suryaturaga3142/stargazing-vr/pcb-stargazing/3dmodels/usb4510-03-1-a.stp

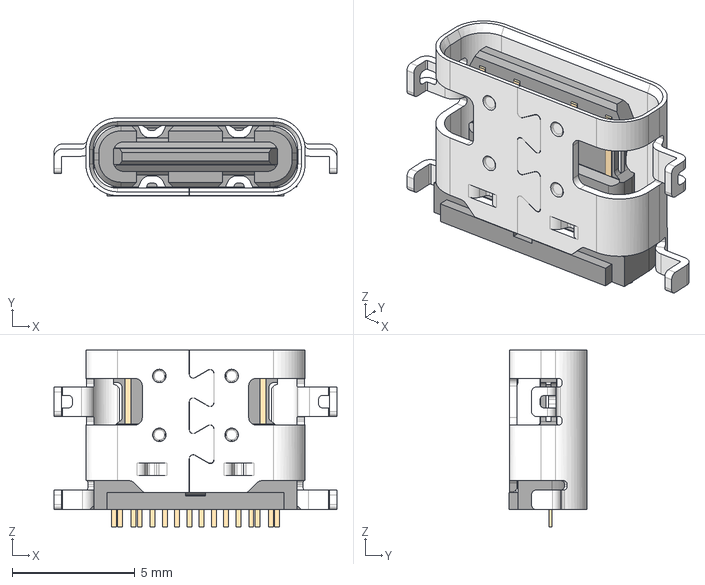
[picture p11: CAD file, 2025-11-23]
pcb-stargazing/3dmodels/usb4510-03-1-a.stp
11.5 x 3.18 x 7.20 mm
