suryaturaga3142/stargazing-vr/include/drivers/imu.h

/*******************************************************************************
 * @file        imu.h
 * @brief       Driver library for IMU.
 * @details     All functions needed to interact with BNO080 IMU.
 * 
 * @see         imu.c for implementation details.
 * 
 * @author      LED Chasers
 * @date        2025-10-14
 * @version     1.0
 ******************************************************************************/

#ifndef IMU_H
#define IMU_H

#include <stdbool.h>
#include "structs.h"
#include "config.h"

#ifdef __cplusplus
extern "C" {
#endif
    
extern volatile bool g_imu_data_ready;          // Set by IMU ISR when new data is available
extern volatile IMUData_t g_latest_imu_data;      // Updated by main reading

bool imu_init(void);
bool imu_check_and_read(void);
bool imu_recenter_yaw(void);

#ifdef __cplusplus
}
#endif

#endif /* IMU_H */
